Coloryr/ColorAudio/src/lib_src/bluez-alsa/src/a2dp-aptx.c

/*
 * BlueALSA - a2dp-aptx.c
 * SPDX-FileCopyrightText: 2016-2025 BlueALSA developers
 * SPDX-License-Identifier: MIT
 */

#include "a2dp-aptx.h"

#if HAVE_CONFIG_H
# include <config.h>
#endif

#include <errno.h>
#include <pthread.h>
#include <stdbool.h>
#include <stddef.h>
#include <stdint.h>
#include <string.h>
#include <unistd.h>

#include "a2dp.h"
#include "ba-config.h"
#include "ba-transport.h"
#include "ba-transport-pcm.h"
#include "codec-aptx.h"
#include "error.h"
#include "io.h"
#include "shared/a2dp-codecs.h"
#include "shared/defs.h"
#include "shared/ffb.h"
#include "shared/log.h"
#include "shared/rt.h"

static const struct a2dp_bit_mapping a2dp_aptx_channels[] = {
	{ APTX_CHANNEL_MODE_MONO, .ch = { 1, a2dp_channel_map_mono } },
	{ APTX_CHANNEL_MODE_STEREO, .ch = { 2, a2dp_channel_map_stereo } },
	{ 0 }
};

static const struct a2dp_bit_mapping a2dp_aptx_rates[] = {
	{ APTX_SAMPLING_FREQ_16000, { 16000 } },
	{ APTX_SAMPLING_FREQ_32000, { 32000 } },
	{ APTX_SAMPLING_FREQ_44100, { 44100 } },
	{ APTX_SAMPLING_FREQ_48000, { 48000 } },
	{ 0 }
};

static void a2dp_aptx_caps_intersect(
		void *capabilities,
		const void *mask) {
	a2dp_caps_bitwise_intersect(capabilities, mask, sizeof(a2dp_aptx_t));
}

static error_code_t a2dp_aptx_caps_foreach_channel_mode(
		const void *capabilities,
		enum a2dp_stream stream,
		a2dp_bit_mapping_foreach_func func,
		void *userdata) {
	const a2dp_aptx_t *caps = capabilities;
	if (stream == A2DP_MAIN)
		return a2dp_bit_mapping_foreach(a2dp_aptx_channels, caps->channel_mode, func, userdata);
	return ERROR_CODE_INVALID_STREAM;
}

static error_code_t a2dp_aptx_caps_foreach_sample_rate(
		const void *capabilities,
		enum a2dp_stream stream,
		a2dp_bit_mapping_foreach_func func,
		void *userdata) {
	const a2dp_aptx_t *caps = capabilities;
	if (stream == A2DP_MAIN)
		return a2dp_bit_mapping_foreach(a2dp_aptx_rates, caps->sampling_freq, func, userdata);
	return ERROR_CODE_INVALID_STREAM;
}

static void a2dp_aptx_caps_select_channel_mode(
		void *capabilities,
		enum a2dp_stream stream,
		unsigned int channels) {
	a2dp_aptx_t *caps = capabilities;
	if (stream == A2DP_MAIN)
		caps->channel_mode = a2dp_bit_mapping_lookup_value(a2dp_aptx_channels,
				caps->channel_mode, channels);
}

static void a2dp_aptx_caps_select_sample_rate(
		void *capabilities,
		enum a2dp_stream stream,
		unsigned int rate) {
	a2dp_aptx_t *caps = capabilities;
	if (stream == A2DP_MAIN)
		caps->sampling_freq = a2dp_bit_mapping_lookup_value(a2dp_aptx_rates,
				caps->sampling_freq, rate);
}

static struct a2dp_caps_helpers a2dp_aptx_caps_helpers = {
	.intersect = a2dp_aptx_caps_intersect,
	.has_stream = a2dp_caps_has_main_stream_only,
	.foreach_channel_mode = a2dp_aptx_caps_foreach_channel_mode,
	.foreach_sample_rate = a2dp_aptx_caps_foreach_sample_rate,
	.select_channel_mode = a2dp_aptx_caps_select_channel_mode,
	.select_sample_rate = a2dp_aptx_caps_select_sample_rate,
};

void *a2dp_aptx_enc_thread(struct ba_transport_pcm *t_pcm) {

	pthread_setcancelstate(PTHREAD_CANCEL_DISABLE, NULL);
	pthread_cleanup_push(PTHREAD_CLEANUP(ba_transport_pcm_thread_cleanup), t_pcm);

	struct ba_transport *t = t_pcm->t;
	struct io_poll io = { .timeout = -1 };

	HANDLE_APTX handle;
	if ((handle = aptxenc_init()) == NULL) {
		error("Couldn't initialize apt-X encoder: %s", strerror(errno));
		goto fail_init;
	}

	ffb_t bt = { 0 };
	ffb_t pcm = { 0 };
	pthread_cleanup_push(PTHREAD_CLEANUP(ffb_free), &bt);
	pthread_cleanup_push(PTHREAD_CLEANUP(ffb_free), &pcm);
	pthread_cleanup_push(PTHREAD_CLEANUP(aptxenc_destroy), handle);

	const unsigned int channels = t_pcm->channels;
	const size_t aptx_frame_len = 2 * sizeof(uint16_t);
	const size_t aptx_frame_pcm_samples = 4 * channels;

	const size_t mtu_write_aptx_frames = t->mtu_write / aptx_frame_len;
	if (ffb_init_int16_t(&pcm, aptx_frame_pcm_samples * mtu_write_aptx_frames) == -1 ||
			ffb_init_uint8_t(&bt, t->mtu_write) == -1) {
		error("Couldn't create data buffers: %s", strerror(errno));
		goto fail_ffb;
	}

	debug_transport_pcm_thread_loop(t_pcm, "START");
	for (ba_transport_pcm_state_set_running(t_pcm);;) {

		switch (io_poll_and_read_pcm(&io, t_pcm, &pcm)) {
		case -1:
			if (errno == ESTALE)
				continue;
			error("PCM poll and read error: %s", strerror(errno));
			/* fall-through */
		case 0:
			ba_transport_stop_if_no_clients(t);
			continue;
		}

		const int16_t *input = pcm.data;
		const size_t samples = ffb_len_out(&pcm);
		size_t input_samples = samples;

		/* Encode and transfer obtained data. */
		while (input_samples >= aptx_frame_pcm_samples) {

			size_t output_len = ffb_len_in(&bt);
			size_t pcm_samples = 0;

			/* Generate as many apt-X frames as possible to fill the output buffer
			 * without overflowing it. The size of the output buffer is based on
			 * the socket MTU, so such a transfer should be most efficient. */
			while (input_samples >= aptx_frame_pcm_samples && output_len >= aptx_frame_len) {

				size_t encoded = output_len;
				ssize_t len;

				if ((len = aptxenc_encode(handle, input, input_samples, bt.tail, &encoded)) <= 0) {
					error("Apt-X encoding error: %s", strerror(errno));
					break;
				}

				input += len;
				input_samples -= len;
				ffb_seek(&bt, encoded);
				output_len -= encoded;
				pcm_samples += len;

			}

			ssize_t len = ffb_blen_out(&bt);
			if ((len = io_bt_write(t_pcm, bt.data, len)) <= 0) {
				if (len == -1)
					error("BT write error: %s", strerror(errno));
				goto fail;
			}

			if (!io.initiated) {
				/* Get the delay due to codec processing. */
				t_pcm->processing_delay_dms = asrsync_get_dms_since_last_sync(&io.asrs);
				// ba_transport_pcm_delay_sync(t_pcm, BA_DBUS_PCM_UPDATE_DELAY);
				io.initiated = true;
			}

			/* Keep data transfer at a constant bit rate. */
			asrsync_sync(&io.asrs, pcm_samples / channels);

			/* reinitialize output buffer */
			ffb_rewind(&bt);

		}

		/* If the input buffer was not consumed (due to codesize limit), we
		 * have to append new data to the existing one. Since we do not use
		 * ring buffer, we will simply move unprocessed data to the front
		 * of our linear buffer. */
		ffb_shift(&pcm, samples - input_samples);

	}

fail:
	debug_transport_pcm_thread_loop(t_pcm, "EXIT");
fail_ffb:
	pthread_cleanup_pop(1);
	pthread_cleanup_pop(1);
	pthread_cleanup_pop(1);
fail_init:
	pthread_cleanup_pop(1);
	return NULL;
}

#if HAVE_APTX_DECODE
__attribute__ ((weak))
void *a2dp_aptx_dec_thread(struct ba_transport_pcm *t_pcm) {

	pthread_setcancelstate(PTHREAD_CANCEL_DISABLE, NULL);
	pthread_cleanup_push(PTHREAD_CLEANUP(ba_transport_pcm_thread_cleanup), t_pcm);

	struct ba_transport *t = t_pcm->t;
	struct io_poll io = { .timeout = -1 };

	HANDLE_APTX handle;
	if ((handle = aptxdec_init()) == NULL) {
		error("Couldn't initialize apt-X decoder: %s", strerror(errno));
		goto fail_init;
	}

	ffb_t bt = { 0 };
	ffb_t pcm = { 0 };
	pthread_cleanup_push(PTHREAD_CLEANUP(ffb_free), &bt);
	pthread_cleanup_push(PTHREAD_CLEANUP(ffb_free), &pcm);
	pthread_cleanup_push(PTHREAD_CLEANUP(aptxdec_destroy), handle);

	/* Note, that we are allocating space for one extra output packed, which is
	 * required by the aptx_decode_sync() function of libopenaptx library. */
	if (ffb_init_int16_t(&pcm, (t->mtu_read / 4 + 1) * 8) == -1 ||
			ffb_init_uint8_t(&bt, t->mtu_read) == -1) {
		error("Couldn't create data buffers: %s", strerror(errno));
		goto fail_ffb;
	}

	debug_transport_pcm_thread_loop(t_pcm, "START");
	for (ba_transport_pcm_state_set_running(t_pcm);;) {

		ssize_t len;
		ffb_rewind(&bt);
		if ((len = io_poll_and_read_bt(&io, t_pcm, &bt)) <= 0) {
			if (len == -1)
				error("BT poll and read error: %s", strerror(errno));
			goto fail;
		}

		if (!ba_transport_pcm_is_active(t_pcm))
			continue;

		uint8_t *input = bt.data;
		size_t input_len = len;

		ffb_rewind(&pcm);
		while (input_len >= 4) {

			size_t decoded = ffb_len_in(&pcm);
			if ((len = aptxdec_decode(handle, input, input_len, pcm.tail, &decoded)) <= 0) {
				error("Apt-X decoding error: %s", strerror(errno));
				continue;
			}

			input += len;
			input_len -= len;
			ffb_seek(&pcm, decoded);

		}

		const size_t samples = ffb_len_out(&pcm);
		io_pcm_scale(t_pcm, pcm.data, samples);
		if (io_pcm_write(t_pcm, pcm.data, samples) == -1)
			error("PCM write error: %s", strerror(errno));

	}

fail:
	debug_transport_pcm_thread_loop(t_pcm, "EXIT");
fail_ffb:
	pthread_cleanup_pop(1);
	pthread_cleanup_pop(1);
	pthread_cleanup_pop(1);
fail_init:
	pthread_cleanup_pop(1);
	return NULL;
}
#endif

static error_code_t a2dp_aptx_configuration_select(
		const struct a2dp_sep *sep,
		void *capabilities) {

	a2dp_aptx_t *caps = capabilities;
	const a2dp_aptx_t saved = *caps;

	/* Narrow capabilities to values supported by BlueALSA. */
	a2dp_aptx_caps_intersect(caps, &sep->config.capabilities);

	unsigned int sampling_freq = 0;
	if (a2dp_aptx_caps_foreach_sample_rate(caps, A2DP_MAIN,
				a2dp_bit_mapping_foreach_get_best_sample_rate, &sampling_freq) == ERROR_CODE_OK)
		caps->sampling_freq = sampling_freq;
	else {
		error("apt-X: No supported sample rates: %#x", saved.sampling_freq);
		return ERROR_CODE_A2DP_NOT_SUPPORTED_SAMPLE_RATE;
	}

	unsigned int channel_mode = 0;
	if (a2dp_aptx_caps_foreach_channel_mode(caps, A2DP_MAIN,
				a2dp_bit_mapping_foreach_get_best_channel_mode, &channel_mode) == ERROR_CODE_OK)
		caps->channel_mode = channel_mode;
	else {
		error("apt-X: No supported channel modes: %#x", saved.channel_mode);
		return ERROR_CODE_A2DP_NOT_SUPPORTED_CHANNEL_MODE;
	}

	return ERROR_CODE_OK;
}

static error_code_t a2dp_aptx_configuration_check(
		const struct a2dp_sep *sep,
		const void *configuration) {

	const a2dp_aptx_t *conf = configuration;
	a2dp_aptx_t conf_v = *conf;

	/* Validate configuration against BlueALSA capabilities. */
	a2dp_aptx_caps_intersect(&conf_v, &sep->config.capabilities);

	if (a2dp_bit_mapping_lookup(a2dp_aptx_rates, conf_v.sampling_freq) == -1) {
		debug("apt-X: Invalid sample rate: %#x", conf->sampling_freq);
		return ERROR_CODE_A2DP_INVALID_SAMPLE_RATE;
	}

	if (a2dp_bit_mapping_lookup(a2dp_aptx_channels, conf_v.channel_mode) == -1) {
		debug("apt-X: Invalid channel mode: %#x", conf->channel_mode);
		return ERROR_CODE_A2DP_INVALID_CHANNEL_MODE;
	}

	return ERROR_CODE_OK;
}

static int a2dp_aptx_transport_init(struct ba_transport *t) {

	ssize_t channels_i;
	if ((channels_i = a2dp_bit_mapping_lookup(a2dp_aptx_channels,
					t->media.a2dp.configuration.aptx.channel_mode)) == -1)
		return -1;

	ssize_t rate_i;
	if ((rate_i = a2dp_bit_mapping_lookup(a2dp_aptx_rates,
					t->media.a2dp.configuration.aptx.sampling_freq)) == -1)
		return -1;

	t->media.pcm.format = BA_TRANSPORT_PCM_FORMAT_S16_2LE;
	t->media.pcm.channels = a2dp_aptx_channels[channels_i].value;
	t->media.pcm.rate = a2dp_aptx_rates[rate_i].value;

	memcpy(t->media.pcm.channel_map, a2dp_aptx_channels[channels_i].ch.map,
			t->media.pcm.channels * sizeof(*t->media.pcm.channel_map));

	return 0;
}

static error_code_t a2dp_aptx_source_init(struct a2dp_sep *sep) {
	if (config.a2dp.force_mono)
		warn("apt-X: Mono channel mode not supported");
	if (config.a2dp.force_44100)
		sep->config.capabilities.aptx.sampling_freq = APTX_SAMPLING_FREQ_44100;
	return ERROR_CODE_OK;
}

static int a2dp_aptx_source_transport_start(struct ba_transport *t) {
	return ba_transport_pcm_start(&t->media.pcm, a2dp_aptx_enc_thread, "ba-a2dp-aptx");
}

struct a2dp_sep a2dp_aptx_source = {
	.name = "A2DP Source (apt-X)",
	.config = {
		.type = A2DP_SOURCE,
		.codec_id = A2DP_CODEC_VENDOR_ID(APTX_VENDOR_ID, APTX_CODEC_ID),
		.caps_size = sizeof(a2dp_aptx_t),
		.capabilities.aptx = {
			.info = A2DP_VENDOR_INFO_INIT(APTX_VENDOR_ID, APTX_CODEC_ID),
			/* NOTE: Used apt-X library does not support
			 *       single channel (mono) mode. */
			.channel_mode =
				APTX_CHANNEL_MODE_STEREO,
			.sampling_freq =
				APTX_SAMPLING_FREQ_16000 |
				APTX_SAMPLING_FREQ_32000 |
				APTX_SAMPLING_FREQ_44100 |
				APTX_SAMPLING_FREQ_48000,
		},
	},
	.init = a2dp_aptx_source_init,
	.configuration_select = a2dp_aptx_configuration_select,
	.configuration_check = a2dp_aptx_configuration_check,
	.transport_init = a2dp_aptx_transport_init,
	.transport_start = a2dp_aptx_source_transport_start,
	.caps_helpers = &a2dp_aptx_caps_helpers,
};

#if HAVE_APTX_DECODE

static int a2dp_aptx_sink_transport_start(struct ba_transport *t) {
	return ba_transport_pcm_start(&t->media.pcm, a2dp_aptx_dec_thread, "ba-a2dp-aptx");
}

struct a2dp_sep a2dp_aptx_sink = {
	.name = "A2DP Sink (apt-X)",
	.config = {
		.type = A2DP_SINK,
		.codec_id = A2DP_CODEC_VENDOR_ID(APTX_VENDOR_ID, APTX_CODEC_ID),
		.caps_size = sizeof(a2dp_aptx_t),
		.capabilities.aptx = {
			.info = A2DP_VENDOR_INFO_INIT(APTX_VENDOR_ID, APTX_CODEC_ID),
			/* NOTE: Used apt-X library does not support
			 *       single channel (mono) mode. */
			.channel_mode =
				APTX_CHANNEL_MODE_STEREO,
			.sampling_freq =
				APTX_SAMPLING_FREQ_16000 |
				APTX_SAMPLING_FREQ_32000 |
				APTX_SAMPLING_FREQ_44100 |
				APTX_SAMPLING_FREQ_48000,
		},
	},
	.configuration_select = a2dp_aptx_configuration_select,
	.configuration_check = a2dp_aptx_configuration_check,
	.transport_init = a2dp_aptx_transport_init,
	.transport_start = a2dp_aptx_sink_transport_start,
	.caps_helpers = &a2dp_aptx_caps_helpers,
};

#endif
