Coloryr/ColorAudio/src/lib_src/bluez-alsa/src/a2dp.c

/*
 * BlueALSA - a2dp.c
 * SPDX-FileCopyrightText: 2016-2025 BlueALSA developers
 * SPDX-License-Identifier: MIT
 */

#include "a2dp.h"

#if HAVE_CONFIG_H
# include <config.h>
#endif

#include <errno.h>
#include <strings.h>

#if ENABLE_AAC
# include "a2dp-aac.h"
#endif
#if ENABLE_APTX
# include "a2dp-aptx.h"
#endif
#if ENABLE_APTX_HD
# include "a2dp-aptx-hd.h"
#endif
#if ENABLE_FASTSTREAM
# include "a2dp-faststream.h"
#endif
#if ENABLE_LC3PLUS
# include "a2dp-lc3plus.h"
#endif
#if ENABLE_LDAC
# include "a2dp-ldac.h"
#endif
#if ENABLE_LHDC
# include "a2dp-lhdc.h"
#endif
#if ENABLE_MPEG
# include "a2dp-mpeg.h"
#endif
#if ENABLE_OPUS
# include "a2dp-opus.h"
#endif
#include "a2dp-sbc.h"
#include "ba-config.h"
#include "error.h"
#include "shared/a2dp-codecs.h"
#include "shared/log.h"

const enum ba_transport_pcm_channel a2dp_channel_map_mono[] = {
	BA_TRANSPORT_PCM_CHANNEL_MONO,
};

const enum ba_transport_pcm_channel a2dp_channel_map_stereo[] = {
	BA_TRANSPORT_PCM_CHANNEL_FL, BA_TRANSPORT_PCM_CHANNEL_FR,
};

const enum ba_transport_pcm_channel a2dp_channel_map_5_1[] = {
	BA_TRANSPORT_PCM_CHANNEL_FC,
	BA_TRANSPORT_PCM_CHANNEL_FL, BA_TRANSPORT_PCM_CHANNEL_FR,
	BA_TRANSPORT_PCM_CHANNEL_RL, BA_TRANSPORT_PCM_CHANNEL_RR,
	BA_TRANSPORT_PCM_CHANNEL_LFE,
};

const enum ba_transport_pcm_channel a2dp_channel_map_7_1[] = {
	BA_TRANSPORT_PCM_CHANNEL_FC,
	BA_TRANSPORT_PCM_CHANNEL_FL, BA_TRANSPORT_PCM_CHANNEL_FR,
	BA_TRANSPORT_PCM_CHANNEL_SL, BA_TRANSPORT_PCM_CHANNEL_SR,
	BA_TRANSPORT_PCM_CHANNEL_RL, BA_TRANSPORT_PCM_CHANNEL_RR,
	BA_TRANSPORT_PCM_CHANNEL_LFE,
};

/**
 * Callback function which returns bitmask for the best channel mode.
 *
 * Note:
 * The user data passed to a2dp_bit_mapping_foreach() function shall be
 * a pointer to an unsigned integer variable initialized to 0. */
error_code_t a2dp_bit_mapping_foreach_get_best_channel_mode(
		struct a2dp_bit_mapping mapping,
		void *userdata) {

	unsigned int *output = userdata;

	/* Skip multi-channel modes. If desired, multi-channel mode can be selected
	 * manually by the user using the SelectCodec() D-Bus method. */
	if (mapping.value > 2 && *output != 0)
		return ERROR_CODE_OK;

	*output = mapping.bit_value;

	if (config.a2dp.force_mono && mapping.value == 1)
		return ERROR_CODE_OK;

	/* Keep iterating, so the last channel mode will be selected. */
	return ERROR_CODE_CONTINUE;
}

/**
 * Callback function which returns bitmask for the best sample rate.
 *
 * Note:
 * The user data passed to a2dp_bit_mapping_foreach() function shall be
 * a pointer to an unsigned integer variable initialized to 0. */
error_code_t a2dp_bit_mapping_foreach_get_best_sample_rate(
		struct a2dp_bit_mapping mapping,
		void *userdata) {

	unsigned int *output = userdata;

	/* Skip anything above 48000 Hz. If desired, bigger sample rates can be
	 * selected manually by the user using the SelectCodec() D-Bus method. */
	if (mapping.value > 48000 && *output != 0)
		return ERROR_CODE_OK;

	*output = mapping.bit_value;

	if (config.a2dp.force_44100 && mapping.value == 44100)
		return ERROR_CODE_OK;

	/* Keep iterating, so the last sample rate will be selected. */
	return ERROR_CODE_CONTINUE;
}

/**
 * Iterate over A2DP bit-field mappings. */
error_code_t a2dp_bit_mapping_foreach(
		const struct a2dp_bit_mapping *mappings,
		uint32_t bitmask,
		a2dp_bit_mapping_foreach_func func,
		void *userdata) {
	error_code_t err = ERROR_CODE_NOT_FOUND;
	for (size_t i = 0; mappings[i].bit_value != 0; i++)
		if (mappings[i].bit_value & bitmask)
			if ((err = func(mappings[i], userdata)) != ERROR_CODE_CONTINUE)
				return err;
	return err == ERROR_CODE_CONTINUE ? ERROR_CODE_OK : err;
}

/**
 * Lookup for given bit-value in the bit mapping table.
 *
 * @param mappings Zero-terminated array of A2DP mappings.
 * @param bit_value A2DP codec bit-value to be looked up.
 * @return This function returns the index of the mapping, or -1 if mapping
 *   for the given bit-value does not exist. */
ssize_t a2dp_bit_mapping_lookup(
		const struct a2dp_bit_mapping *mappings,
		uint32_t bit_value) {
	for (size_t i = 0; mappings[i].bit_value != 0; i++)
		if (mappings[i].bit_value == bit_value)
			return i;
	return -1;
}

/**
 * Lookup for given value in the bit mapping table.
 *
 * @param mappings Zero-terminated array of A2DP mappings.
 * @param bitmask A2DP codec bitmask for bit-value validation.
 * @param value A2DP codec value to be looked up.
 * @return On success this function returns the bit-value. Otherwise,
 *   0 is returned. */
uint32_t a2dp_bit_mapping_lookup_value(
		const struct a2dp_bit_mapping *mappings,
		uint32_t bitmask,
		unsigned int value) {
	uint32_t bit_value = 0;
	for (size_t i = 0; mappings[i].bit_value != 0; i++)
		if (mappings[i].bit_value & bitmask &&
				mappings[i].value == value)
			bit_value = mappings[i].bit_value;
	return bit_value;
}

/**
 * Simple A2DP capabilities intersection function.
 *
 * This function performs a simple bitwise AND operation on given capabilities
 * and mask. */
void a2dp_caps_bitwise_intersect(
		void * restrict capabilities,
		const void * restrict mask,
		size_t size) {

	const uint8_t *caps_mask = mask;
	uint8_t *caps = capabilities;

	for (size_t i = 0; i < size; i++)
		caps[i] = caps[i] & caps_mask[i];

}

/**
 * Function which returns true only for the main A2DP stream. */
bool a2dp_caps_has_main_stream_only(
		const void *capabilities,
		enum a2dp_stream stream) {
	(void)capabilities;
	return stream == A2DP_MAIN;
}

struct a2dp_sep * const a2dp_seps[] = {
#if ENABLE_OPUS
	// &a2dp_opus_source,
	&a2dp_opus_sink,
#endif
#if ENABLE_LC3PLUS
	// &a2dp_lc3plus_source,
	&a2dp_lc3plus_sink,
#endif
#if ENABLE_LDAC
	// &a2dp_ldac_source,
# if HAVE_LDAC_DECODE
	&a2dp_ldac_sink,
# endif
#endif
#if ENABLE_APTX
	// &a2dp_aptx_source,
# if HAVE_APTX_DECODE
	&a2dp_aptx_sink,
# endif
#endif
#if ENABLE_AAC
	// &a2dp_aac_source,
	&a2dp_aac_sink,
#endif
	// &a2dp_sbc_source,
	&a2dp_sbc_sink,
	NULL,
};

/**
 * Initialize A2DP SEPs. */
error_code_t a2dp_seps_init(void) {

	for (size_t i = 0; a2dp_seps[i] != NULL; i++) {
		/* We want the list of SEPs to be seen as const outside
		 * of this file, so we have to cast it here. */
		struct a2dp_sep *sep = (struct a2dp_sep *)a2dp_seps[i];

		switch (sep->config.type) {
		case A2DP_SINK:
			sep->enabled &= config.profile.a2dp_sink;
			break;
		}

		if (sep->init != NULL && sep->enabled) {
			error_code_t err;
			if ((err = sep->init(sep)) != ERROR_CODE_OK)
				return err;
		}

	}

	return ERROR_CODE_OK;
}

static int a2dp_codec_id_cmp(uint32_t a, uint32_t b) {
	if (a < A2DP_CODEC_VENDOR || b < A2DP_CODEC_VENDOR)
		return a < b ? -1 : (a == b ? 0 : 1);
	const char *a_name;
	if ((a_name = a2dp_codecs_codec_id_to_string(a)) == NULL)
		return 1;
	const char *b_name;
	if ((b_name = a2dp_codecs_codec_id_to_string(b)) == NULL)
		return -1;
	return strcasecmp(a_name, b_name);
}

/**
 * Compare A2DP SEP configurations.
 *
 * This function orders A2DP SEPs according to following rules:
 *  - order SEPs by A2DP type
 *  - order SEPs by codec ID
 *  - order vendor codecs alphabetically (case insensitive) */
int a2dp_sep_config_cmp(
		const struct a2dp_sep_config *a,
		const struct a2dp_sep_config *b) {
	if (a->type == b->type)
		return a2dp_codec_id_cmp(a->codec_id, b->codec_id);
	return a->type - b->type;
}

/**
 * Compare A2DP SEPs. */
int a2dp_sep_ptr_cmp(const struct a2dp_sep **a, const struct a2dp_sep **b) {
	return a2dp_sep_config_cmp(&(*a)->config, &(*b)->config);
}

/**
 * Lookup SEP for given type and codec.
 *
 * @param type The A2DP SEP type.
 * @param codec_id BlueALSA A2DP 32-bit codec ID.
 * @return On success this function returns the address of the SEP
 *   configuration structure. Otherwise, NULL is returned. */
const struct a2dp_sep *a2dp_sep_lookup(enum a2dp_type type, uint32_t codec_id) {
	for (size_t i = 0; a2dp_seps[i] != NULL; i++)
		if (a2dp_seps[i]->config.type == type &&
				a2dp_seps[i]->config.codec_id == codec_id)
			return a2dp_seps[i];
	return NULL;
}

/**
 * Get A2DP 32-bit vendor codec ID - BlueALSA extension.
 *
 * @param capabilities A2DP vendor codec capabilities.
 * @param size A2DP vendor codec capabilities size.
 * @return On success this function returns A2DP 32-bit vendor codec ID. */
uint32_t a2dp_get_vendor_codec_id(const void *capabilities, size_t size) {
	if (size < sizeof(a2dp_vendor_info_t))
		return errno = EINVAL, 0xFFFFFFFF;
	return a2dp_codecs_vendor_codec_id(capabilities);
}

/**
 * Select best possible A2DP codec configuration. */
error_code_t a2dp_select_configuration(
		const struct a2dp_sep *sep,
		void *capabilities,
		size_t size) {

	if (size == sep->config.caps_size)
		return sep->configuration_select(sep, capabilities);

	error("Invalid capabilities size: %zu != %zu", size, sep->config.caps_size);
	return ERROR_CODE_INVALID_SIZE;
}

/**
 * Check whether A2DP configuration is valid.
 *
 * @param sep A2DP Stream End-Point setup.
 * @param configuration A2DP codec configuration blob.
 * @param size The size of the A2DP codec configuration blob.
 * @return On success this function returns ERROR_CODE_OK. Otherwise,
 *   one of the application error codes is returned. */
error_code_t a2dp_check_configuration(
		const struct a2dp_sep *sep,
		const void *configuration,
		size_t size) {

	if (size == sep->config.caps_size)
		return sep->configuration_check(sep, configuration);

	error("Invalid configuration size: %zu != %zu", size, sep->config.caps_size);
	return ERROR_CODE_INVALID_SIZE;
}
