Coloryr/ColorAudio/src/lib_src/bluez-alsa/src/ba-transport.h

/*
 * BlueALSA - ba-transport.h
 * SPDX-FileCopyrightText: 2016-2025 BlueALSA developers
 * SPDX-License-Identifier: MIT
 */

#pragma once
#ifndef BLUEALSA_BATRANSPORT_H_
#define BLUEALSA_BATRANSPORT_H_

#if HAVE_CONFIG_H
# include <config.h>
#endif

#include <pthread.h>
#include <stdbool.h>
#include <stddef.h>
#include <stdint.h>
#include <time.h>

#include <alsa/asoundlib.h>
#include <glib.h>

#include "a2dp.h"
#include "ba-device.h"
#include "ba-transport-pcm.h"
#include "bluez.h"
#include "shared/a2dp-codecs.h"
#include "shared/rc.h"

enum ba_transport_thread_manager_command {
	BA_TRANSPORT_THREAD_MANAGER_TERMINATE = 0,
	BA_TRANSPORT_THREAD_MANAGER_CANCEL_THREADS,
	BA_TRANSPORT_THREAD_MANAGER_CANCEL_IF_NO_CLIENTS,
};

enum ba_transport_profile {
	BA_TRANSPORT_PROFILE_NONE        = 0,
	BA_TRANSPORT_PROFILE_A2DP_SOURCE = (1 << 0),
	BA_TRANSPORT_PROFILE_A2DP_SINK   = (2 << 0),
	BA_TRANSPORT_PROFILE_HFP_HF      = (1 << 4),
	BA_TRANSPORT_PROFILE_HFP_AG      = (2 << 4),
	BA_TRANSPORT_PROFILE_HSP_HS      = (1 << 6),
	BA_TRANSPORT_PROFILE_HSP_AG      = (2 << 6),
};

#define BA_TRANSPORT_PROFILE_MASK_HFP \
	(BA_TRANSPORT_PROFILE_HFP_HF | BA_TRANSPORT_PROFILE_HFP_AG)
#define BA_TRANSPORT_PROFILE_MASK_HSP \
	(BA_TRANSPORT_PROFILE_HSP_HS | BA_TRANSPORT_PROFILE_HSP_AG)
#define BA_TRANSPORT_PROFILE_MASK_AG \
	(BA_TRANSPORT_PROFILE_HSP_AG | BA_TRANSPORT_PROFILE_HFP_AG)
#define BA_TRANSPORT_PROFILE_MASK_HF \
	(BA_TRANSPORT_PROFILE_HSP_HS | BA_TRANSPORT_PROFILE_HFP_HF)

#define BA_TRANSPORT_PROFILE_IS_MEDIA_A2DP(t) \
	((t)->profile & ( \
		BA_TRANSPORT_PROFILE_A2DP_SOURCE | BA_TRANSPORT_PROFILE_A2DP_SINK))

#define BA_TRANSPORT_PROFILE_IS_MEDIA_ASHA(t) false

#define BA_TRANSPORT_PROFILE_IS_MEDIA(t) \
	(BA_TRANSPORT_PROFILE_IS_MEDIA_A2DP(t) || \
	 BA_TRANSPORT_PROFILE_IS_MEDIA_ASHA(t))

#define BA_TRANSPORT_PROFILE_IS_SCO(t) \
	((t)->profile & ( \
		BA_TRANSPORT_PROFILE_MASK_HFP | BA_TRANSPORT_PROFILE_MASK_HSP))

struct ba_transport {
	rc_t _rc;

	/* backward reference to device */
	struct ba_device *d;

	/* Transport structure covers all transports supported by BlueALSA. However,
	 * every transport requires specific handling - link acquisition, transport
	 * specific configuration, freeing resources, etc. */
	enum ba_transport_profile profile;

	/* guard modifications of transport codec */
	pthread_mutex_t codec_id_mtx;
	/* ID of currently selected codec */
	uint32_t codec_id;

	/* synchronization for codec selection */
	pthread_mutex_t codec_select_client_mtx;

	/* data for D-Bus management */
	char *bluez_dbus_owner;
	char *bluez_dbus_path;

	/* guard modifications of our file descriptor
	 * and the IO threads stopping flag */
	pthread_mutex_t bt_fd_mtx;

	/* Ensure BT file descriptor acquisition procedure
	 * is completed atomically. */
	pthread_mutex_t acquisition_mtx;

	/* This field stores a file descriptor (socket) associated with the BlueZ
	 * side of the transport. The role of this socket depends on the transport
	 * type - it can be either A2DP or SCO link. */
	int bt_fd;

	/* max transfer unit values for bt_fd */
	size_t mtu_read;
	size_t mtu_write;

	/* thread for managing IO threads */
	pthread_t thread_manager_thread_id;
	int thread_manager_pipe[2];

	/* indicates IO threads stopping */
	pthread_cond_t stopped_cond;
	bool stopping;

	union {

		struct {

			/* used D-Bus endpoint path */
			const char *bluez_dbus_sep_path;

			/* current state of the transport */
			pthread_cond_t state_changed_cond;
			enum bluez_media_transport_state state;

			/* delay reporting support */
			bool delay_reporting;
			/* delay reported by BlueZ */
			uint16_t delay;
			/* volume reported by BlueZ */
			uint16_t volume;

			struct ba_transport_pcm pcm;
			/* PCM for back-channel stream */
			struct ba_transport_pcm pcm_bc;

			/* Value reported by the ioctl(TIOCOUTQ) when the output buffer is
			 * empty. Somehow this ioctl call reports "available" buffer space.
			 * So, in order to get the number of bytes in the queue buffer, we
			 * have to subtract the initial value from values returned by
			 * subsequent ioctl() calls. */
			int bt_fd_coutq_init;

			union {
				struct {
					/* selected stream endpoint */
					const struct a2dp_sep * sep;
					/* selected codec configuration */
					a2dp_t configuration;
				} a2dp;
			};

		} media;

		struct {

			/* Associated RFCOMM thread for SCO transport handled by local
			 * HSP/HFP implementation. Otherwise, this field is set to NULL. */
			struct ba_rfcomm *rfcomm;

			/* Speaker and microphone signals should to be exposed as
			 * a separate PCM devices. Hence, there is a requirement
			 * for separate configurations.
			 *
			 * NOTE: The speaker/microphone notation always refers to the whole
			 *       AG/HS setup. For AG the speaker is an outgoing audio stream,
			 *       while for HS the speaker is an incoming audio stream. */
			struct ba_transport_pcm pcm_spk;
			struct ba_transport_pcm pcm_mic;

			/* time-stamp when the SCO link has been closed */
			struct timespec closed_at;

		} sco;

	};

	/* callback functions for self-management */
	int (*acquire)(struct ba_transport *);
	int (*release)(struct ba_transport *);

};

struct ba_transport * ba_transport_new_a2dp(
		struct ba_device * device,
		enum ba_transport_profile profile,
		const char * dbus_owner,
		const char * dbus_path,
		const struct a2dp_sep * sep,
		const void * configuration);
struct ba_transport * ba_transport_new_sco(
		struct ba_device * device,
		enum ba_transport_profile profile,
		const char * dbus_owner,
		const char * dbus_path,
		int rfcomm_fd);
#if DEBUG
const char * ba_transport_debug_name(
		const struct ba_transport * t);
#endif

struct ba_transport * ba_transport_lookup(
		const struct ba_device * device,
		const char * dbus_path);
static inline struct ba_transport * ba_transport_ref(
		struct ba_transport * t) {
	return rc_ref(t);
}

void ba_transport_destroy(struct ba_transport * t);
void ba_transport_unref(struct ba_transport * t);

int ba_transport_select_codec_a2dp(
		struct ba_transport *t,
		const struct a2dp_sep_config *remote_sep_cfg,
		const void *configuration);
int ba_transport_select_codec_sco(
		struct ba_transport *t,
		uint8_t codec_id);

uint32_t ba_transport_get_codec(
		const struct ba_transport *t);
void ba_transport_set_codec(
		struct ba_transport *t,
		uint32_t codec_id);

int ba_transport_start(struct ba_transport *t);
int ba_transport_stop(struct ba_transport *t);
int ba_transport_stop_async(struct ba_transport *t);
int ba_transport_stop_if_no_clients(struct ba_transport *t);

int ba_transport_acquire(struct ba_transport *t);
int ba_transport_release(struct ba_transport *t);

int ba_transport_set_media_state(
		struct ba_transport *t,
		enum bluez_media_transport_state state);

#endif
