Coloryr/ColorAudio/src/lib_src/bluez-alsa/src/storage.c

/*
 * BlueALSA - storage.c
 * SPDX-FileCopyrightText: 2022-2025 BlueALSA developers
 * SPDX-License-Identifier: MIT
 */

#include "storage.h"

#include <errno.h>
#include <pthread.h>
#include <stdbool.h>
#include <stdint.h>
#include <stdio.h>
#include <stdlib.h>
#include <string.h>
#include <sys/stat.h>

#include <bluetooth/bluetooth.h>

#include <glib.h>

#include "ba-transport.h"
#include "hfp.h"
#include "utils.h"
#include "shared/a2dp-codecs.h"
#include "shared/defs.h"
#include "shared/log.h"

#define BA_STORAGE_KEY_CLIENT_DELAYS    "ClientDelays"
#define BA_STORAGE_KEY_SOFT_VOLUME      "SoftVolume"
#define BA_STORAGE_KEY_VOLUME           "Volume"
#define BA_STORAGE_KEY_MUTE             "Mute"

struct storage {
	/* remote BT device address */
	bdaddr_t addr;
	/* associated storage file */
	GKeyFile *keyfile;
};

static char storage_root_dir[128];
static pthread_mutex_t storage_mutex = PTHREAD_MUTEX_INITIALIZER;
static GHashTable *storage_map = NULL;

static struct storage *storage_lookup(const bdaddr_t *addr) {
	return g_hash_table_lookup(storage_map, addr);
}

static struct storage *storage_new(const bdaddr_t *addr) {

	struct storage *st;
	/* return existing storage if it exists */
	if ((st = storage_lookup(addr)) != NULL)
		goto final;

	if ((st = malloc(sizeof(*st))) == NULL)
		goto final;

	bacpy(&st->addr, addr);
	st->keyfile = g_key_file_new();

	/* Insert a new storage into the map. Please, note that the key is a pointer
	 * to memory stored in the value structure. This is fine as long as the value
	 * is not replaced during key insertion. In such case the old (dangling) key
	 * pointer might/will be used to access the new value! */
	g_hash_table_insert(storage_map, &st->addr, st);

final:
	return st;
}

static void storage_free(struct storage *st) {
	if (st == NULL)
		return;
	g_key_file_free(st->keyfile);
	free(st);
}

/**
 * Initialize BlueALSA persistent storage.
 *
 * @param root The root directory for the persistent storage.
 * @return On success this function returns 0. Otherwise -1 is returned. */
int storage_init(const char *root) {

	debug("Initializing persistent storage: %s", root);

	strncpy(storage_root_dir, root, sizeof(storage_root_dir) - 1);
	if (mkdir(storage_root_dir, S_IRWXU) == -1 && errno != EEXIST)
		warn("Couldn't create directory: %s: %s", storage_root_dir, strerror(errno));

	if (storage_map == NULL)
		storage_map = g_hash_table_new_full(g_bdaddr_hash, g_bdaddr_equal,
				NULL, (GDestroyNotify)storage_free);

	return 0;
}

/**
 * Cleanup resources allocated by the persistent storage. */
void storage_destroy(void) {
	if (storage_map == NULL)
		return;
	g_hash_table_unref(storage_map);
	storage_map = NULL;
}

/**
 * Load persistent storage file for the given BT device. */
int storage_device_load(const struct ba_device *d) {

	char addrstr[18];
	char path[sizeof(storage_root_dir) + sizeof(addrstr)];
	ba2str(&d->addr, addrstr);
	snprintf(path, sizeof(path), "%s/%s", storage_root_dir, addrstr);
	int rv = -1;

	pthread_mutex_lock(&storage_mutex);

	debug("Loading storage: %s", path);

	struct storage *st;
	if ((st = storage_new(&d->addr)) == NULL)
		goto final;

	GError *err = NULL;
	if (!g_key_file_load_from_file(st->keyfile, path, G_KEY_FILE_NONE, &err)) {
		if (err->code != G_FILE_ERROR_NOENT)
			warn("Couldn't load storage: %s: %s", path, err->message);
		g_error_free(err);
		goto final;
	}

	rv = 0;

final:
	pthread_mutex_unlock(&storage_mutex);
	return rv;
}

/**
 * Save persistent storage file for the given BT device. */
int storage_device_save(const struct ba_device *d) {

	char addrstr[18];
	char path[sizeof(storage_root_dir) + sizeof(addrstr)];
	ba2str(&d->addr, addrstr);
	snprintf(path, sizeof(path), "%s/%s", storage_root_dir, addrstr);
	int rv = -1;

	pthread_mutex_lock(&storage_mutex);

	struct storage *st;
	if ((st = storage_lookup(&d->addr)) == NULL)
		goto final;

	debug("Saving storage: %s", path);

	GError *err = NULL;
	if (!g_key_file_save_to_file(st->keyfile, path, &err)) {
		error("Couldn't save storage: %s: %s", path, err->message);
		g_error_free(err);
		goto final;
	}

	/* remove the storage from the map */
	g_hash_table_remove(storage_map, &d->addr);

	rv = 0;

final:
	pthread_mutex_unlock(&storage_mutex);
	return rv;
}

/**
 * Clear persistent storage for the given BT device. */
int storage_device_clear(const struct ba_device *d) {

	int rv = -1;

	pthread_mutex_lock(&storage_mutex);

	struct storage *st;
	if ((st = storage_lookup(&d->addr)) == NULL)
		goto final;

	g_key_file_free(st->keyfile);
	st->keyfile = g_key_file_new();

	rv = 0;

final:
	pthread_mutex_unlock(&storage_mutex);
	return rv;
}

/**
 * Load PCM client delays to the hash table. */
static GHashTable *storage_pcm_data_load_delays(GKeyFile *db, const char *group,
		const struct ba_transport_pcm *pcm) {

	const struct ba_transport *t = pcm->t;
	GHashTable *delays = g_hash_table_new(NULL, NULL);

	size_t length = 0;
	char **list = g_key_file_get_string_list(db, group,
			BA_STORAGE_KEY_CLIENT_DELAYS, &length, NULL);

	for (size_t i = 0; i < length; i++) {
		char *codec_name = list[i];
		char *value = strchr(list[i], ':');
		if (value == NULL)
			continue;
		/* Split string into a codec name and delay value. */
		*value++ = '\0';
		uint32_t codec_id = 0xFFFFFFFF;
		if (BA_TRANSPORT_PROFILE_IS_MEDIA(t) &&
				(codec_id = a2dp_codecs_codec_id_from_string(codec_name)) == 0xFFFFFFFF)
			continue;
		if (BA_TRANSPORT_PROFILE_IS_SCO(t) &&
				(codec_id = hfp_codec_id_from_string(codec_name)) == HFP_CODEC_UNDEFINED)
			continue;
		const int16_t delay = atoi(value);
		g_hash_table_insert(delays, GINT_TO_POINTER(codec_id), GINT_TO_POINTER(delay));
	}

	g_strfreev(list);
	return delays;
}

static int storage_pcm_data_sync_delay(GKeyFile *db, const char *group,
		struct ba_transport_pcm *pcm) {

	const struct ba_transport *t = pcm->t;
	int rv = 0;

	GHashTable *delays = storage_pcm_data_load_delays(db, group, pcm);

	void *value = NULL;
	const uint32_t codec_id = t->codec_id;
	if (g_hash_table_lookup_extended(delays, GINT_TO_POINTER(codec_id), NULL, &value)) {
		/* If the right codec was found, sync the client delay. */
		pcm->client_delay_dms = GPOINTER_TO_INT(value);
		rv = 1;
	}

	g_hash_table_unref(delays);
	return rv;
}

static int storage_pcm_data_sync_volume(GKeyFile *db, const char *group,
		struct ba_transport_pcm *pcm) {

	const size_t channels = pcm->channels;
	int *list_volume;
	gboolean *list_mute;
	gsize len;
	int rv = 0;

	if (g_key_file_has_key(db, group, BA_STORAGE_KEY_SOFT_VOLUME, NULL)) {
		pcm->soft_volume = g_key_file_get_boolean(db, group,
				BA_STORAGE_KEY_SOFT_VOLUME, NULL);
		rv = 1;
	}

	if ((list_volume = g_key_file_get_integer_list(db, group,
					BA_STORAGE_KEY_VOLUME, &len, NULL)) != NULL &&
			len <= ARRAYSIZE(pcm->volume)) {
		for (size_t i = 0; i < len; i++)
			ba_transport_pcm_volume_set(&pcm->volume[i], &list_volume[i], NULL, NULL);
		/* Upscale volume for the rest of the channels if needed. */
		for (size_t i = len; i < channels; i++)
			ba_transport_pcm_volume_set(&pcm->volume[i], &list_volume[0], NULL, NULL);
		rv = 1;
	}

	if ((list_mute = g_key_file_get_boolean_list(db, group,
					BA_STORAGE_KEY_MUTE, &len, NULL)) != NULL &&
			len <= ARRAYSIZE(pcm->volume)) {
		for (size_t i = 0; i < len; i++) {
			const bool mute = list_mute[i];
			ba_transport_pcm_volume_set(&pcm->volume[i], NULL, &mute, NULL);
		}
		const bool mute = list_mute[0];
		/* Upscale mute for the rest of the channels if needed. */
		for (size_t i = len; i < channels; i++)
			ba_transport_pcm_volume_set(&pcm->volume[i], NULL, &mute, NULL);
		rv = 1;
	}

	g_free(list_volume);
	g_free(list_mute);
	return rv;
}

/**
 * Synchronize PCM with persistent storage.
 *
 * @param pcm The PCM structure to synchronize.
 * @return This function returns 1 or 0 respectively if the storage data was
 *   synchronized or not. On error -1 is returned. */
int storage_pcm_data_sync(struct ba_transport_pcm *pcm) {

	const struct ba_transport *t = pcm->t;
	const struct ba_device *d = t->d;
	int rv = 0;

	pthread_mutex_lock(&storage_mutex);

	struct storage *st;
	if ((st = storage_lookup(&d->addr)) == NULL)
		goto final;

	GKeyFile *keyfile = st->keyfile;
	const char *group = pcm->ba_dbus_path;

	if (!g_key_file_has_group(keyfile, group))
		goto final;

	if (storage_pcm_data_sync_delay(keyfile, group, pcm))
		rv = 1;
	if (storage_pcm_data_sync_volume(keyfile, group, pcm))
		rv = 1;

final:
	pthread_mutex_unlock(&storage_mutex);
	return rv;
}

static void storage_pcm_data_update_delay(GKeyFile *db, const char *group,
		const struct ba_transport_pcm *pcm) {

	const struct ba_transport *t = pcm->t;

	GHashTable *delays = storage_pcm_data_load_delays(db, group, pcm);
	/* Update the delay value for the current codec. */
	g_hash_table_insert(delays, GINT_TO_POINTER(t->codec_id),
			GINT_TO_POINTER(pcm->client_delay_dms));

	const size_t num_codecs = g_hash_table_size(delays);
	char **list = calloc(num_codecs + 1, sizeof(char *));

	GHashTableIter iter;
	g_hash_table_iter_init(&iter, delays);

	size_t index = 0;
	void *key, *value;
	while (g_hash_table_iter_next(&iter, &key, &value)) {
		if (GPOINTER_TO_INT(value) == 0)
			/* Do not store the delay if it is zero. */
			continue;
		const char *codec = NULL;
		if (BA_TRANSPORT_PROFILE_IS_MEDIA(t))
			codec = a2dp_codecs_codec_id_to_string(GPOINTER_TO_INT(key));
		if (BA_TRANSPORT_PROFILE_IS_SCO(t))
			codec = hfp_codec_id_to_string(GPOINTER_TO_INT(key));
		if (codec == NULL)
			continue;
		list[index] = malloc(strlen(codec) + 1 + 6 + 1);
		sprintf(list[index], "%s:%d", codec, GPOINTER_TO_INT(value));
		index++;
	}

	g_key_file_set_string_list(db, group, BA_STORAGE_KEY_CLIENT_DELAYS,
		(const char * const *)list, num_codecs);

	g_hash_table_unref(delays);
	for (size_t i = 0; i < num_codecs; i++)
		free(list[i]);
	free(list);

}

static void storage_pcm_data_update_volume(GKeyFile *db, const char *group,
		const struct ba_transport_pcm *pcm) {

	const size_t channels = pcm->channels;
	gboolean mute[ARRAYSIZE(pcm->volume)];
	int volume[ARRAYSIZE(pcm->volume)];

	for (size_t i = 0; i < channels; i++) {
		mute[i] = pcm->volume[i].soft_mute;
		volume[i] = pcm->volume[i].level;
	}

	g_key_file_set_boolean(db, group, BA_STORAGE_KEY_SOFT_VOLUME, pcm->soft_volume);
	g_key_file_set_integer_list(db, group, BA_STORAGE_KEY_VOLUME, volume, channels);
	g_key_file_set_boolean_list(db, group, BA_STORAGE_KEY_MUTE, mute, channels);

}

/**
 * Update persistent storage with PCM data.
 *
 * @param pcm The PCM structure for which to update the storage.
 * @return On success this function returns 0. Otherwise -1 is returned. */
int storage_pcm_data_update(const struct ba_transport_pcm *pcm) {

	const struct ba_transport *t = pcm->t;
	const struct ba_device *d = t->d;
	int rv = -1;

	pthread_mutex_lock(&storage_mutex);

	struct storage *st;
	if ((st = storage_lookup(&d->addr)) == NULL)
		if ((st = storage_new(&d->addr)) == NULL)
			goto final;

	GKeyFile *keyfile = st->keyfile;
	const char *group = pcm->ba_dbus_path;

	storage_pcm_data_update_delay(keyfile, group, pcm);
	storage_pcm_data_update_volume(keyfile, group, pcm);

	rv = 0;

final:
	pthread_mutex_unlock(&storage_mutex);
	return rv;
}
