Coloryr/ColorAudio/src/lib_src/bluez-alsa/src/ba-transport-pcm.h

/*
 * BlueALSA - ba-transport-pcm.h
 * SPDX-FileCopyrightText: 2016-2025 BlueALSA developers
 * SPDX-License-Identifier: MIT
 */

#pragma once
#ifndef BLUEALSA_BATRANSPORTPCM_H_
#define BLUEALSA_BATRANSPORTPCM_H_

#if HAVE_CONFIG_H
# include <config.h>
#endif

#include <pthread.h>
#include <stdbool.h>
#include <stdint.h>

#include <glib.h>

enum ba_transport_pcm_mode {
	/* PCM used for capturing audio */
	BA_TRANSPORT_PCM_MODE_SOURCE,
	/* PCM used for playing audio */
	BA_TRANSPORT_PCM_MODE_SINK,
};

enum ba_transport_pcm_state {
	BA_TRANSPORT_PCM_STATE_IDLE,
	BA_TRANSPORT_PCM_STATE_STARTING,
	BA_TRANSPORT_PCM_STATE_RUNNING,
	BA_TRANSPORT_PCM_STATE_STOPPING,
	BA_TRANSPORT_PCM_STATE_JOINING,
	BA_TRANSPORT_PCM_STATE_TERMINATED,
};

/**
 * Builder for 16-bit PCM stream format identifier. */
#define BA_TRANSPORT_PCM_FORMAT(sign, width, bytes, endian) \
	(((sign & 1) << 15) | ((endian & 1) << 14) | ((bytes & 0x3F) << 8) | (width & 0xFF))

#define BA_TRANSPORT_PCM_FORMAT_SIGN(format)   (((format) >> 15) & 0x1)
#define BA_TRANSPORT_PCM_FORMAT_WIDTH(format)  ((format) & 0xFF)
#define BA_TRANSPORT_PCM_FORMAT_BYTES(format)  (((format) >> 8) & 0x3F)
#define BA_TRANSPORT_PCM_FORMAT_ENDIAN(format) (((format) >> 14) & 0x1)

#define BA_TRANSPORT_PCM_FORMAT_U8      BA_TRANSPORT_PCM_FORMAT(0, 8, 1, 0)
#define BA_TRANSPORT_PCM_FORMAT_S16_2LE BA_TRANSPORT_PCM_FORMAT(1, 16, 2, 0)
#define BA_TRANSPORT_PCM_FORMAT_S24_3LE BA_TRANSPORT_PCM_FORMAT(1, 24, 3, 0)
#define BA_TRANSPORT_PCM_FORMAT_S24_4LE BA_TRANSPORT_PCM_FORMAT(1, 24, 4, 0)
#define BA_TRANSPORT_PCM_FORMAT_S32_4LE BA_TRANSPORT_PCM_FORMAT(1, 32, 4, 0)

enum ba_transport_pcm_channel {
	BA_TRANSPORT_PCM_CHANNEL_MONO, /* mono */
	BA_TRANSPORT_PCM_CHANNEL_FL,   /* front left */
	BA_TRANSPORT_PCM_CHANNEL_FR,   /* front right */
	BA_TRANSPORT_PCM_CHANNEL_FC,   /* front center */
	BA_TRANSPORT_PCM_CHANNEL_RL,   /* rear left */
	BA_TRANSPORT_PCM_CHANNEL_RR,   /* rear right */
	BA_TRANSPORT_PCM_CHANNEL_SL,   /* side left */
	BA_TRANSPORT_PCM_CHANNEL_SR,   /* side right */
	BA_TRANSPORT_PCM_CHANNEL_LFE,  /* low frequency effects */
};

struct ba_transport_pcm_volume {
	/* volume level change in "dB * 100" */
	int level;
	/* audio signal mute switches */
	bool soft_mute;
	bool hard_mute;
	/* calculated PCM scale factor based on decibel formula
	 * pow(10, dB / 20); for muted channel it shall equal 0 */
	double scale;
};

enum ba_transport_pcm_signal {
	BA_TRANSPORT_PCM_SIGNAL_OPEN,
	BA_TRANSPORT_PCM_SIGNAL_CLOSE,
	BA_TRANSPORT_PCM_SIGNAL_PAUSE,
	BA_TRANSPORT_PCM_SIGNAL_RESUME,
	BA_TRANSPORT_PCM_SIGNAL_DRAIN,
	BA_TRANSPORT_PCM_SIGNAL_DROP,
};

struct ba_transport;

struct ba_transport_pcm {

	/* backward reference to transport */
	struct ba_transport *t;

	/* PCM stream operation mode */
	enum ba_transport_pcm_mode mode;
	/* indicates a master PCM */
	bool master;

	/* guard PCM data updates */
	pthread_mutex_t mutex;
	/* updates notification */
	pthread_cond_t cond;

	pthread_mutex_t state_mtx;
	/* current state of the PCM */
	enum ba_transport_pcm_state state;

	/* PCM file descriptor */
	int fd;
	/* clone of BT socket */
	int fd_bt;

	/* indicates whether PCM is running */
	bool paused;

	/* 16-bit stream format identifier */
	uint16_t format;
	/* number of audio channels */
	unsigned int channels;
	/* PCM sample rate */
	unsigned int rate;

	/* Delay caused by the codec due to internal buffering. The delay is
	 * expressed in 1/10 of millisecond. */
	unsigned int codec_delay_dms;
	/* Delay caused by data processing. This delay component depends on
	 * the host computational power. It is used to compensate for the time
	 * required to encode or decode audio. */
	unsigned int processing_delay_dms;
	/* The last reported total codec + processing delay. It is used to limit
	 * the rate at which changes are reported via D-Bus. */
	unsigned int reported_codec_delay_dms;
	/* Positive (or negative) delay reported by the client. */
	int client_delay_dms;
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
